Timurksz/Bidirectional-Four-Switch-Buck-Boot-Converter/Guctek_FSBB/hardware/symbol_footprint_step/step/G12AP.stp

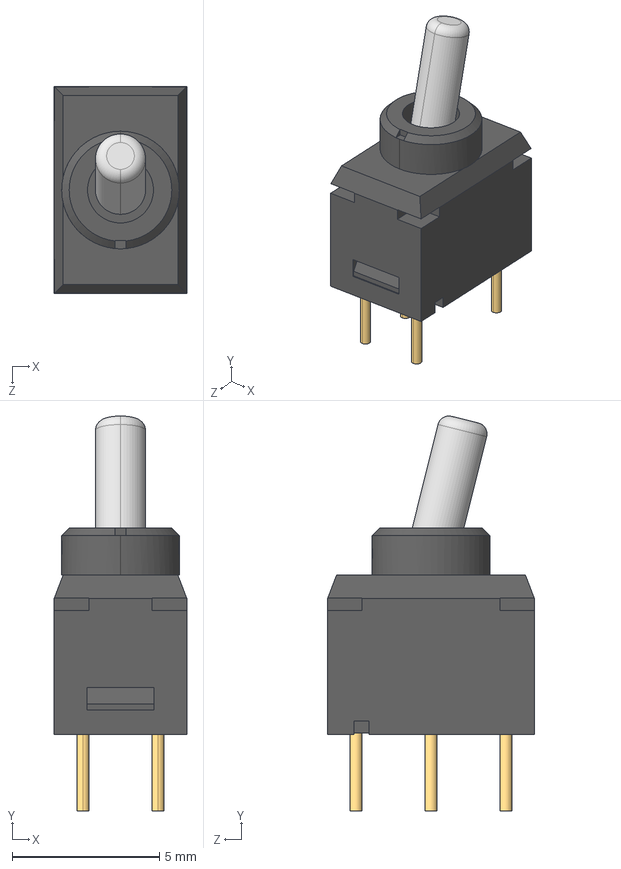
[picture p19: CAD file, 2026-05-19]
Guctek_FSBB/hardware/symbol_footprint_step/step/G12AP.stp
4.50 x 13.4 x 7.01 mm
GP-body
G-actuator
G1P-trmnls
