Timurksz/Bidirectional-Four-Switch-Buck-Boot-Converter/Guctek_FSBB/hardware/symbol_footprint_step/step/SKRKAEE010.stp

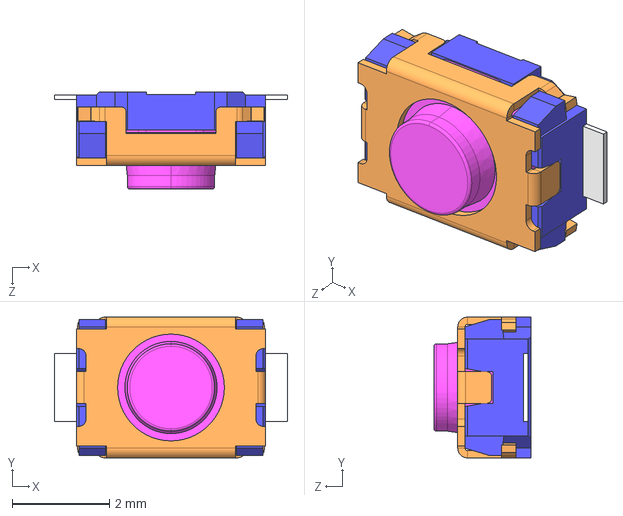
[picture p20: CAD file, 2026-05-19]
Guctek_FSBB/hardware/symbol_footprint_step/step/SKRKAEE010.stp
4.80 x 2.90 x 2.00 mm
