Timurksz/Bidirectional-Four-Switch-Buck-Boot-Converter/Guctek_FSBB/hardware/symbol_footprint_step/step/SS510.stp

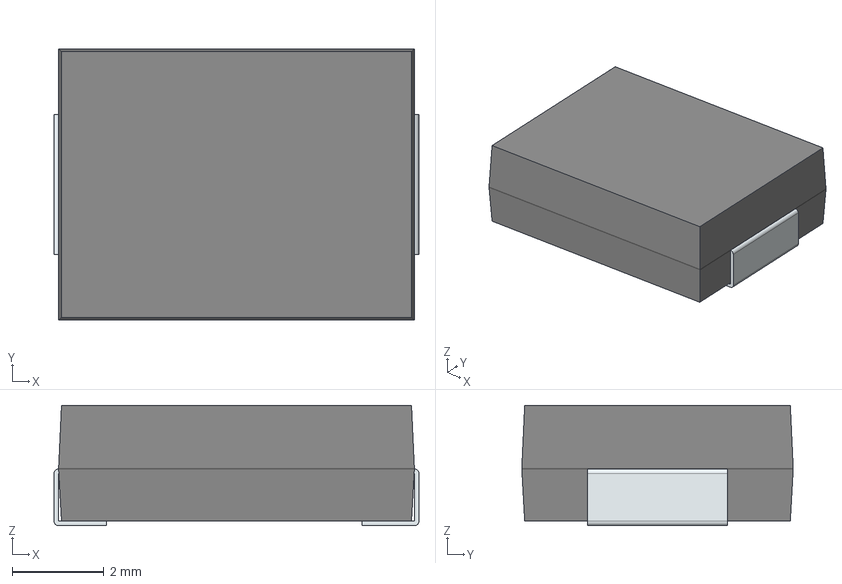
[picture p21: CAD file, 2026-05-19]
Guctek_FSBB/hardware/symbol_footprint_step/step/SS510.stp
7.94 x 5.91 x 2.62 mm
FilletPin1
FilletPin2
