Timurksz/Bidirectional-Four-Switch-Buck-Boot-Converter/Guctek_FSBB/hardware/symbol_footprint_step/step/5103308-1.step

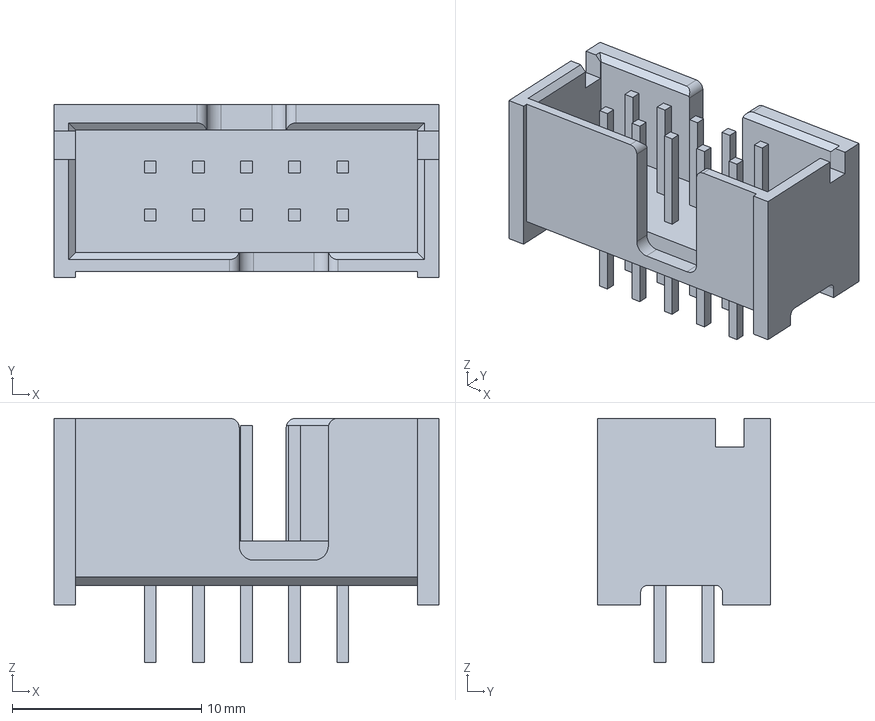
[picture p22: CAD file, 2026-05-19]
Guctek_FSBB/hardware/symbol_footprint_step/step/5103308-1.step
20.3 x 9.14 x 12.9 mm
